monkbroc/logomatic/Software/firmware/LZWFunctions.cpp

/*
 * Animated GIFs Display Code for SmartMatrix and 32x32 RGB LED Panels
 *
 * This file contains code to decompress the LZW encoded animated GIF data
 *
 * Written by: Craig A. Lindley, Fabrice Bellard and Steven A. Bennett
 * See my book, "Practical Image Processing in C", John Wiley & Sons, Inc.
 *
 * Copyright (c) 2014 Craig A. Lindley
 * Minor modifications by Louis Beaudoin (pixelmatix)
 *
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
 * THE SOFTWARE IS PROVIDED "AS IS", WITHOUT WARRANTY OF ANY KIND, EXPRESS OR
 * IMPLIED, INCLUDING BUT NOT LIMITED TO THE WARRANTIES OF MERCHANTABILITY, FITNESS
 * FOR A PARTICULAR PURPOSE AND NONINFRINGEMENT. IN NO EVENT SHALL THE AUTHORS OR
 * COPYRIGHT HOLDERS BE LIABLE FOR ANY CLAIM, DAMAGES OR OTHER LIABILITY, WHETHER
 * IN AN ACTION OF CONTRACT, TORT OR OTHERWISE, ARISING FROM, OUT OF OR IN
 * CONNECTION WITH THE SOFTWARE OR THE USE OR OTHER DEALINGS IN THE SOFTWARE.
 */

#include "Particle.h"
#include "GIFDecoder.h"

// LZW constants
// NOTE: LZW_MAXBITS set to 11 (initially 10) to support more GIFs with 6k RAM increase
#define LZW_MAXBITS    11
#define LZW_SIZTABLE  (1 << LZW_MAXBITS)

// Masks for 0 .. 16 bits
unsigned int mask[17] = {
    0x0000, 0x0001, 0x0003, 0x0007,
    0x000F, 0x001F, 0x003F, 0x007F,
    0x00FF, 0x01FF, 0x03FF, 0x07FF,
    0x0FFF, 0x1FFF, 0x3FFF, 0x7FFF,
    0xFFFF
};

// LZW variables
static byte *pbuf;
static int bbits;
static int bbuf;
static int cursize;                // The current code size
static int curmask;
static int codesize;
static int clear_code;
static int end_code;
static int newcodes;               // First available code
static int top_slot;               // Highest code for current size
static int slot;                   // Last read code
static int fc, oc;
static int bs;                     // Current buffer size for GIF
static byte *sp;
static byte stack  [LZW_SIZTABLE];
static byte suffix [LZW_SIZTABLE];
static unsigned int prefix [LZW_SIZTABLE];

// Initialize LZW decoder
//   csize initial code size in bits
//   buf input data
void lzw_decode_init (int csize, byte *buf) {

    // Initialize read buffer variables
    pbuf = buf;
    bbuf = 0;
    bbits = 0;
    bs = 0;

    // Initialize decoder variables
    codesize = csize;
    cursize = codesize + 1;
    curmask = mask[cursize];
    top_slot = 1 << cursize;
    clear_code = 1 << codesize;
    end_code = clear_code + 1;
    slot = newcodes = clear_code + 2;
    oc = fc = -1;
    sp = stack;
}

//  Get one code of given number of bits from stream
int lzw_get_code() {

    while (bbits < cursize) {
        if (!bs) {
            bs = *pbuf++;
        }
        bbuf |= (*pbuf++) << bbits;
        bbits += 8;
        bs--;
    }
    int c = bbuf;
    bbuf >>= cursize;
    bbits -= cursize;
    return c & curmask;
}

// Decode given number of bytes
//   buf 8 bit output buffer
//   len number of pixels to decode
//   returns the number of bytes decoded
int lzw_decode(byte *buf, int len) {
    int l, c, code;

    if (end_code < 0) {
        return 0;
    }
    l = len;

    for (;;) {
        while (sp > stack) {
            *buf++ = *(--sp);
            if ((--l) == 0) {
                return len;
            }
        }
        c = lzw_get_code();
        if (c == end_code) {
            break;

        }
        else if (c == clear_code) {
            cursize = codesize + 1;
            curmask = mask[cursize];
            slot = newcodes;
            top_slot = 1 << cursize;
            fc= oc= -1;

        }
        else	{

            code = c;
            if ((code == slot) && (fc >= 0)) {
                *sp++ = fc;
                code = oc;
            }
            else if (code >= slot) {
                break;
            }
            while (code >= newcodes) {
                *sp++ = suffix[code];
                code = prefix[code];
            }
            *sp++ = code;
            if ((slot < top_slot) && (oc >= 0)) {
                suffix[slot] = code;
                prefix[slot++] = oc;
            }
            fc = code;
            oc = c;
            if (slot >= top_slot) {
                if (cursize < LZW_MAXBITS) {
                    top_slot <<= 1;
                    curmask = mask[++cursize];
                }

            }
        }
    }
    end_code = -1;
    return len - l;
}
