monkbroc/logomatic/Software/prototype/rainbow.cpp

/*
 * This is a minimal example, see extra-examples.cpp for a version
 * with more explantory documentation, example routines, how to
 * hook up your pixels and all of the pixel types that are supported.
 *
 */

#include "application.h"
#include "neopixel.h" // use for local build

SYSTEM_THREAD(ENABLED);

// IMPORTANT: Set pixel COUNT, PIN and TYPE
#define PIXEL_PIN A7
#define PIXEL_COUNT 60
#define PIXEL_TYPE WS2812B

Adafruit_NeoPixel strip = Adafruit_NeoPixel(PIXEL_COUNT, PIXEL_PIN, PIXEL_TYPE);

// Prototypes for local build, ok to leave in for Build IDE
void rainbow(uint8_t wait);
uint32_t Wheel(byte WheelPos);

void setup()
{
  Serial.begin(9600);
  delay(1000);
  Serial.println("Starting");
  strip.begin();
  strip.show(); // Initialize all pixels to 'off'
}
void loop()
{
  rainbow(20);
}

void rainbow(uint8_t wait) {
  uint16_t i, j;

  for(j=0; j<256; j++) {
    for(i=0; i<strip.numPixels(); i++) {
      strip.setPixelColor(i, Wheel((i+j) & 255));
    }
    strip.show();
    Serial.println("Show " + String(j, DEC));
    delay(wait);
  }
}

// Input a value 0 to 255 to get a color value.
// The colours are a transition r - g - b - back to r.
uint32_t Wheel(byte WheelPos) {
  if(WheelPos < 85) {
   return strip.Color(WheelPos * 3, 255 - WheelPos * 3, 0);
  } else if(WheelPos < 170) {
   WheelPos -= 85;
   return strip.Color(255 - WheelPos * 3, 0, WheelPos * 3);
  } else {
   WheelPos -= 170;
   return strip.Color(0, WheelPos * 3, 255 - WheelPos * 3);
  }
}
